bakadave/fanControl/PCB/fanControl/simulation/Vin_mon_WCA.asc

C1: cap; 10n
M2: pmos; BSS84
Q1: npn; BC847B
R1: res; {WC1(1k,0.05,4)}
R2: res; {WC1(22k,0.01,5)}
R3: res; {WC1(22k,0.01,1)}
R4: res; {WC1(10k,0.05,2)}
R5: res; {WC1(10k,0.05,3)}
R6: res; {WC1(470R,0.05,6)}
V1: voltage; 12
V2: voltage; V={if(V(Vin)>7,5.5,0)}
V3: voltage; {STEPPING}
Named nets: 0, Vin_mon, PSU_en, Vin, B, G, E, D, S, STEPPING
.dc V1 0 40 0.1
.tran 5m startup
https://electronics.stackexchange.com/questions/546121/placement-of-mosfets-in-switchable-voltage-divider-for-voltage-measurements
***********************************************************
*
* BZX84-C3V3
*
* Nexperia
*
* Voltage regulator diodes
* VFmax = 0,9V    @ IF = 10mA
* IRmax = 5µA     @ VR = 1V
* VZmax = 3,5V    @ IZ = 5mA
* IZSM  = 6A      @ tp = 100µs
*
*
*
* Package pinning does not match Spice model pinning.
* Package: SOT23
*
* Package Pin 1: Anode
* Package Pin 2: Not Connected
* Package Pin 3: Cathode
*
*
* Extraction date (week/year): #
* Simulator: PSPICE
*
***********************************************************
*
.MODEL BZX84-C3V3 D
+ IS = 7.035E-16
+ N = 0.9809
+ BV = 3.3
+ IBV = 0.005
+ RS = 0.3487
+ CJO = 3.162E-10
+ VJ = 0.6687
+ M = 0.3164
+ FC = 0.5
.ENDS
*
.FUNC MOD(a,b) {a-FLOOR(a/b)*b}
.FUNC BIT(x) {if(MOD(STEPPING,2**(X+1))>=2**x,1,0)}
.FUNC EVA1 (nom, tol, param_num) {if(STEPPING == -1, nom, nom*(1-tol)+2*nom*tol*BIT(param_num))}
.FUNC EVA2 (nom, min, max, param_num) {if(STEPPING == -1, nom, IF(BIT(param_num),max,min))}
.FUNC WC1 (nom, tol, param_num) EVA1(nom, tol, param_num)
.FUNC WC2 (nom, min, max, param_num) EVA2(nom, min, max, param_num)
.step param STEPPING -1 63 1
**********************************************************
*
* BC847
*
* Nexperia
*
* General purpose NPN transistor
* IC   = 100 mA
* VCEO = 45 V 
* hFE  = 110 - 450 @ 5V/2mA
* 
*
*
*
* Package pinning does not match Spice model pinning.
* Package: SOT 23
* 
* Package Pin 1: Base
* Package Pin 2: Emitter
* Package Pin 3: Collector
* 
*
* Extraction date (week/year): 24/2021
* Spicemodel includes temperature dependency
*
**********************************************************
*#
*
* Diode D1, Transistor Q2 and resistor RQ 
* are dedicated to improve modeling of quasi
* saturation area and reverse mode operation
* and do not reflect physical devices.
*
.SUBCKT BC847A 1 2 3
Q1 1 2 3 MAIN 0.8636
Q2 11 2 33 MAIN 0.1364
RQ 11 1 324.8
D1 2 1 DIODE
*
.MODEL MAIN NPN
+ IS = 1.124E-14
+ NF = 0.9872
+ ISE = 2.566E-15
+ NE = 1.661
+ BF = {WC2(110,180,220,0)}
+ IKF = 0.09455
+ VAF = 36.27
+ NR = 0.9859
+ ISC = 7.015E-18
+ NC = 0.9228
+ BR = 7.047
+ IKR = 0.8167
+ VAR = 16.61
+ RB = 150
+ IRB = 0.0008356
+ RBM = 0.8289
+ RE = 0.804
+ RC = 0.2454
+ XTB = 1.382
+ EG = 1.11
+ XTI = 7.452
+ CJE = 1.264E-11
+ VJE = 0.7056
+ MJE = 0.3401
+ TF = 6.258E-10
+ XTF = 25
+ VTF = 2
+ ITF = 0.277
+ PTF = 0
+ CJC = 3.624E-12
+ VJC = 0.5036
+ MJC = 0.365
+ XCJC = 1
+ TR = 1.55E-07
+ CJS = 0
+ VJS = 0.75
+ MJS = 0.333
+ FC = 0.78
.MODEL DIODE D
+ IS = 1.365E-15
+ N = 0.988
+ BV = 1000
+ IBV = 0.001
+ RS = 2163
+ CJO = 0
+ VJ = 1
+ M = 0.5
+ FC = 0
+ TT = 0
+ EG = 1.11
+ XTI = 3
.ENDS
**********************************************************
*
* BC847
*
* Nexperia
*
* General purpose NPN transistor
* IC   = 100 mA
* VCEO = 45 V 
* hFE  = 110 - 450 @ 5V/2mA
* 
*
*
*
* Package pinning does not match Spice model pinning.
* Package: SOT 23
* 
* Package Pin 1: Base
* Package Pin 2: Emitter
* Package Pin 3: Collector
* 
*
* Extraction date (week/year): 24/2021
* Spicemodel includes temperature dependency
*
**********************************************************
*#
*
* Diode D1, Transistor Q2 and resistor RQ 
* are dedicated to improve modeling of quasi
* saturation area and reverse mode operation
* and do not reflect physical devices.
*
.SUBCKT BC847B 1 2 3
Q1 1 2 3 MAIN 0.8636
Q2 11 2 33 MAIN 0.1364
RQ 11 1 324.8
D1 2 1 DIODE
*
.MODEL MAIN NPN
+ IS = 1.124E-14
+ NF = 0.9872
+ ISE = 2.566E-15
+ NE = 1.661
+ BF = {WC2(290,200,450,0)}
+ IKF = 0.09455
+ VAF = 36.27
+ NR = 0.9859
+ ISC = 7.015E-18
+ NC = 0.9228
+ BR = 7.047
+ IKR = 0.8167
+ VAR = 16.61
+ RB = 150
+ IRB = 0.0008356
+ RBM = 0.8289
+ RE = 0.804
+ RC = 0.2454
+ XTB = 1.382
+ EG = 1.11
+ XTI = 7.452
+ CJE = 1.264E-11
+ VJE = 0.7056
+ MJE = 0.3401
+ TF = 6.258E-10
+ XTF = 25
+ VTF = 2
+ ITF = 0.277
+ PTF = 0
+ CJC = 3.624E-12
+ VJC = 0.5036
+ MJC = 0.365
+ XCJC = 1
+ TR = 1.55E-07
+ CJS = 0
+ VJS = 0.75
+ MJS = 0.333
+ FC = 0.78
.MODEL DIODE D
+ IS = 1.365E-15
+ N = 0.988
+ BV = 1000
+ IBV = 0.001
+ RS = 2163
+ CJO = 0
+ VJ = 1
+ M = 0.5
+ FC = 0
+ TT = 0
+ EG = 1.11
+ XTI = 3
.ENDS
**********************************************************
*
* BC847
*
* Nexperia
*
* General purpose NPN transistor
* IC   = 100 mA
* VCEO = 45 V 
* hFE  = 110 - 450 @ 5V/2mA
* 
*
*
*
* Package pinning does not match Spice model pinning.
* Package: SOT 23
* 
* Package Pin 1: Base
* Package Pin 2: Emitter
* Package Pin 3: Collector
* 
*
* Extraction date (week/year): 24/2021
* Spicemodel includes temperature dependency
*
**********************************************************
*#
*
* Diode D1, Transistor Q2 and resistor RQ 
* are dedicated to improve modeling of quasi
* saturation area and reverse mode operation
* and do not reflect physical devices.
*
.SUBCKT BC847C 1 2 3
Q1 1 2 3 MAIN 0.8636
Q2 11 2 33 MAIN 0.1364
RQ 11 1 324.8
D1 2 1 DIODE
*
.MODEL MAIN NPN
+ IS = 1.124E-14
+ NF = 0.9872
+ ISE = 2.566E-15
+ NE = 1.661
+ BF = {WC2(420,520,800,0)}
+ IKF = 0.09455
+ VAF = 36.27
+ NR = 0.9859
+ ISC = 7.015E-18
+ NC = 0.9228
+ BR = 7.047
+ IKR = 0.8167
+ VAR = 16.61
+ RB = 150
+ IRB = 0.0008356
+ RBM = 0.8289
+ RE = 0.804
+ RC = 0.2454
+ XTB = 1.382
+ EG = 1.11
+ XTI = 7.452
+ CJE = 1.264E-11
+ VJE = 0.7056
+ MJE = 0.3401
+ TF = 6.258E-10
+ XTF = 25
+ VTF = 2
+ ITF = 0.277
+ PTF = 0
+ CJC = 3.624E-12
+ VJC = 0.5036
+ MJC = 0.365
+ XCJC = 1
+ TR = 1.55E-07
+ CJS = 0
+ VJS = 0.75
+ MJS = 0.333
+ FC = 0.78
.MODEL DIODE D
+ IS = 1.365E-15
+ N = 0.988
+ BV = 1000
+ IBV = 0.001
+ RS = 2163
+ CJO = 0
+ VJ = 1
+ M = 0.5
+ FC = 0
+ TT = 0
+ EG = 1.11
+ XTI = 3
.ENDS
