bakadave/fanControl/PCB/fanControl/simulation/Draft2.asc

M1: pmos; DMP4065S
Q1: npn; BC847B
R1: res; 50
R2: res; {WC1(10k,0.05,3)}
R3: res; {WC1(1k,0.05,4)}
R4: res; {WC1(22k,0.01,1)}
R5: res; {WC1(10k,0.05,2)}
V1: voltage; 12
V2: voltage; PULSE(0 5 1m 10u 10u 3m)
V3: voltage; {STEPPING}
Named nets: 0, G, S, D, STEPPING
.tran 5m startup
*---------- DMP4065S Spice Model ----------
.SUBCKT DMP4065S 10 20 30 
*     TERMINALS:  D  G  S
M1 1 2 3 3 PMOS L = 1E-006 W = 1E-006 
RD 10 1 0.04289 
RS 30 3 0.001 
RG 20 2 10.24 
CGS 2 3 5.75E-010 
EGD 12 30 2 1 1 
VFB 14 30 0 
FFB 2 1 VFB 1 
CGD 13 14 4.5E-010 
R1 13 30 1 
D1 13 12 DLIM 
DDG 14 15 DCGD 
R2 12 15 1 
D2 30 15 DLIM 
DSD 10 3 DSUB 
.MODEL PMOS PMOS LEVEL = 3 U0 = 400 VMAX = 1E+006 ETA = 0.001 
+ TOX = 6E-008 NSUB = 1E+016 KP = 8.015 KAPPA = 19.32 VTO = -1.585 
.MODEL DCGD D CJO = 1.7E-010 VJ = 0.8 M = 0.6 
.MODEL DSUB D IS = 2.364E-010 N = 1.26 RS = 0.0254 BV = 46 CJO = 2.226E-010 VJ = 0.8 M = 0.6 
.MODEL DLIM D IS = 0.0001 
.ENDS
*Diodes DMP4065S Spice Model v1.0M Last Revised 2018/2/1
.FUNC MOD(a,b) {a-FLOOR(a/b)*b}
.FUNC BIT(x) {if(MOD(STEPPING,2**(X+1))>=2**x,1,0)}
.FUNC EVA1 (nom, tol, param_num) {if(STEPPING == -1, nom, nom*(1-tol)+2*nom*tol*BIT(param_num))}
.FUNC EVA2 (nom, min, max, param_num) {if(STEPPING == -1, nom, IF(BIT(param_num),max,min))}
.FUNC WC1 (nom, tol, param_num) EVA1(nom, tol, param_num)
.FUNC WC2 (nom, min, max, param_num) EVA2(nom, min, max, param_num)
.step param STEPPING -1 31 1
**********************************************************
*
* BC847
*
* Nexperia
*
* General purpose NPN transistor
* IC   = 100 mA
* VCEO = 45 V 
* hFE  = 110 - 450 @ 5V/2mA
* 
*
*
*
* Package pinning does not match Spice model pinning.
* Package: SOT 23
* 
* Package Pin 1: Base
* Package Pin 2: Emitter
* Package Pin 3: Collector
* 
*
* Extraction date (week/year): 24/2021
* Spicemodel includes temperature dependency
*
**********************************************************
*#
*
* Diode D1, Transistor Q2 and resistor RQ 
* are dedicated to improve modeling of quasi
* saturation area and reverse mode operation
* and do not reflect physical devices.
*
.SUBCKT BC847B 1 2 3
Q1 1 2 3 MAIN 0.8636
Q2 11 2 33 MAIN 0.1364
RQ 11 1 324.8
D1 2 1 DIODE
*
.MODEL MAIN NPN
+ IS = 1.124E-14
+ NF = 0.9872
+ ISE = 2.566E-15
+ NE = 1.661
+ BF = {WC2(290,200,450,0)}
+ IKF = 0.09455
+ VAF = 36.27
+ NR = 0.9859
+ ISC = 7.015E-18
+ NC = 0.9228
+ BR = 7.047
+ IKR = 0.8167
+ VAR = 16.61
+ RB = 150
+ IRB = 0.0008356
+ RBM = 0.8289
+ RE = 0.804
+ RC = 0.2454
+ XTB = 1.382
+ EG = 1.11
+ XTI = 7.452
+ CJE = 1.264E-11
+ VJE = 0.7056
+ MJE = 0.3401
+ TF = 6.258E-10
+ XTF = 25
+ VTF = 2
+ ITF = 0.277
+ PTF = 0
+ CJC = 3.624E-12
+ VJC = 0.5036
+ MJC = 0.365
+ XCJC = 1
+ TR = 1.55E-07
+ CJS = 0
+ VJS = 0.75
+ MJS = 0.333
+ FC = 0.78
.MODEL DIODE D
+ IS = 1.365E-15
+ N = 0.988
+ BV = 1000
+ IBV = 0.001
+ RS = 2163
+ CJO = 0
+ VJ = 1
+ M = 0.5
+ FC = 0
+ TT = 0
+ EG = 1.11
+ XTI = 3
.ENDS
