bakadave/fanControl/PCB/fanControl/simulation/LDO_rev_prot.asc

C1: cap; 10µ; Rser=200m
C2: cap; 10µ; Rser=200m
C3: cap; 100n; Rser=10
D1: schottky; VS-10BQ015-M3
D2: schottky; CUS10S30
R1: res; 25
R2: res; 10k
U1: LT1117-3.3
V1: voltage; SINE(5 25m 4k); Rser=100m
V2: voltage; 3.3
Named nets: 0
********************************
* Copyright: *
* Vishay Intertechnology, Inc. *
********************************
*95666VS-10BQ015-M3
********************************
* Model Diode *
********************************************
.MODEL VS-10BQ015-M3 D
+ IS=3.0000E-6
+ N=.85237
+ RS=36.273E-3
+ IKF=.91313
+ XTI=2
+ CJO=467.42E-12
+ M=.47867
+ VJ=.3905
+ ISR=33.566E-6
+ NR=4.9950
+ BV=36
+ IBV=10.000E-3
*T_MEASURED=25
.ENDS VS-10BQ015-M3
.tran 10m startup
*********************************************************************
*  (C)  Copyright  TOSHIBA CORPORATION  2016
*  Date                 :15/09/2016
*  File Name            :CUS10S30.lib
*  Part Number          :CUS10S30
*  Parameter Ver.       :Ver.1
*  Simulator            :PSpice
*  Model Call Name      :CUS10S30
*  TNOM                 :25 degree
*  Pin Assign           :1=Anode 2=Cathode
*********************************************************************
.SUBCKT CUS10S30 1 2
D1 11 2 CUS10S30
J1 1 11 11 j1
R1 11 2 1E+15
.MODEL CUS10S30 D (
+ IS = 1.8338e-005
+ N = 0.94847
+ RS = 0.025763
+ BV = 30
+ IBV = 1E-10
+ CJO = 1.3454e-010
+ M = 0.66446
+ VJ = 0.75954
+ TT = 0
+ TNOM = 25
+ XTI = -20.7786 )
.MODEL j1 NJF (
+ VTO = -15
+ BETA = 0.09713
+ LAMBDA = 50.6489
+ VTOTC = 0.1079
+ TNOM = 25 )
.ENDS
