bakadave/fanControl/PCB/fanControl/simulation/Draft1.asc

C1: cap; 47µ; V=25
C2: cap; 200n
C3: cap; 50µ
C4: cap; 1µ; V=200
C5: cap; 2µ; V=200
Q1: npn; BC846B
Q2: pnp; BC856B
R1: res; 430
R2: res; 5k1
R3: res; 180k
R4: res; 62k
R5: res; 21
R_load: res; 100
V1: voltage; 12
V2: voltage; ""
Named nets: V+, 0
MIC
.tran 1m
