bakadave/fanControl/PCB/fanControl/simulation/low_power_cutoff.asc

C2: cap; 47µ; V=35
D1: zener; BZX84C6V8L
Q1: npn; BC547B
R5: res; 10k
R6: res; 47k
R8: res; 10k
V1: voltage; PULSE(0 32 4m 5m 5m 5m); Rser=0.1
Named nets: 0, Q1_Vc, Q1_Vb, V_out
.tran 0 15m 0 100u startup
.dc V1 0 40 0.1
