bakadave/fanControl/PCB/fanControl/simulation/microphone_circuit.asc

C1: cap; 47µ; V=25
C2: cap; 100n
C3: cap; 1n
M1: nmos; Si7336ADP
Q1: npn; BC846B
Q2: pnp; BC856B
R1: res; 430
R2: res; 5k1
R3: res; 180k
R4: res; 62k
R5: res; 21
R_load: res; 10
V1: voltage; 12
V2: voltage; ""; AC 1
Named nets: 0
MIC
.tran 1m
.ac oct 10 20 20k
